ikajdan/reflow_hot_plate/data/calculations/differential_pair.png

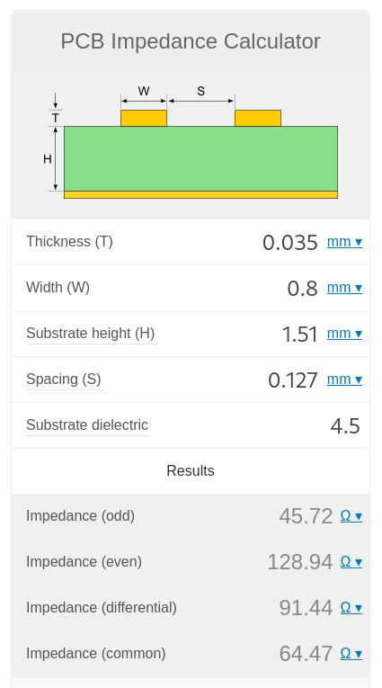
data/calculations/differential_pair.png
