ikajdan/reflow_hot_plate/data/calculations/heatbed_80x80.png

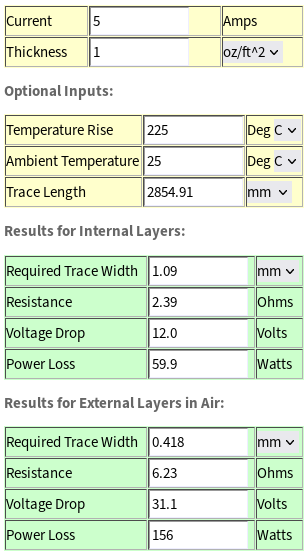
data/calculations/heatbed_80x80.png
