ikajdan/reflow_hot_plate/firmware/Components/FSM/Src/fsm.c

/**
 ******************************************************************************
 * @file           : fsm.c
 * @brief          : Finite-state machine library
 *
 ******************************************************************************
 */

/* Includes ------------------------------------------------------------------*/
#include "fsm.h"
#include <stddef.h>

/* Typedefs ------------------------------------------------------------------*/

/* Defines -------------------------------------------------------------------*/

/* Macros --------------------------------------------------------------------*/

/* Private variables ---------------------------------------------------------*/

/* Public variables ----------------------------------------------------------*/
FSM_Handle_TypeDef hfsm = {
        .state = FSM_WELCOME,
        .stage = FSM_HEATING_PRE,
        .duration = 0,
        .profile_duration = 0,
        .error_duration = 0,
        .tc_temperature = 0,
        .rtd_temperature = 0,
        .temperature = 0,
        .target_temperature = 0,
        .output = 0.0f,
        .name = "None",
        .stages = { 0 },
        .profile = { 0 },
};

/* Private function prototypes -----------------------------------------------*/

/* Public function prototypes ------------------------------------------------*/

/* Private functions ---------------------------------------------------------*/

/* Public functions ----------------------------------------------------------*/
void FSM_SetActiveProfile(MENU_Handle_TypeDef *hmenu, FSM_Handle_TypeDef *hfsm)
{
    hfsm->name = hmenu->selected_item->profile_name;
    hfsm->stages = hmenu->selected_item->profile_stages;
    hfsm->profile_duration = hmenu->selected_item->profile_duration;
    hfsm->profile = hmenu->selected_item->profile;
}
